inria-paris-robotics-lab/wireless-e-stop/images/NANO-nRF24L01.png

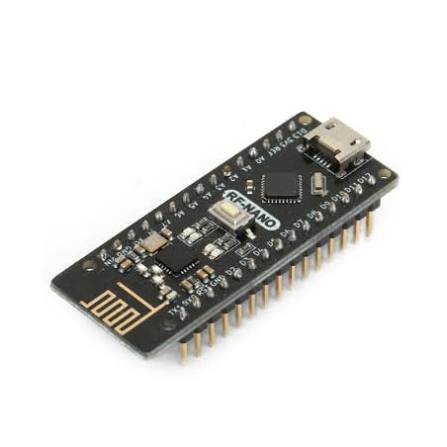
images/NANO-nRF24L01.png
