inria-paris-robotics-lab/wireless-e-stop/images/ws2812B.png

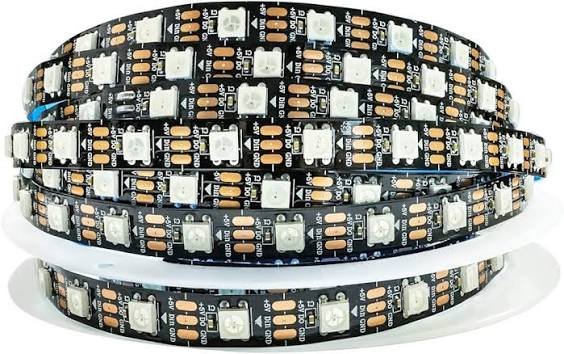
images/ws2812B.png
