inria-paris-robotics-lab/wireless-e-stop/hardware/Elec_schem/receiver/receiver.kicad_sch

## KiCad design hardware/Elec_schem/receiver/receiver.kicad_sch (2026-09-03)

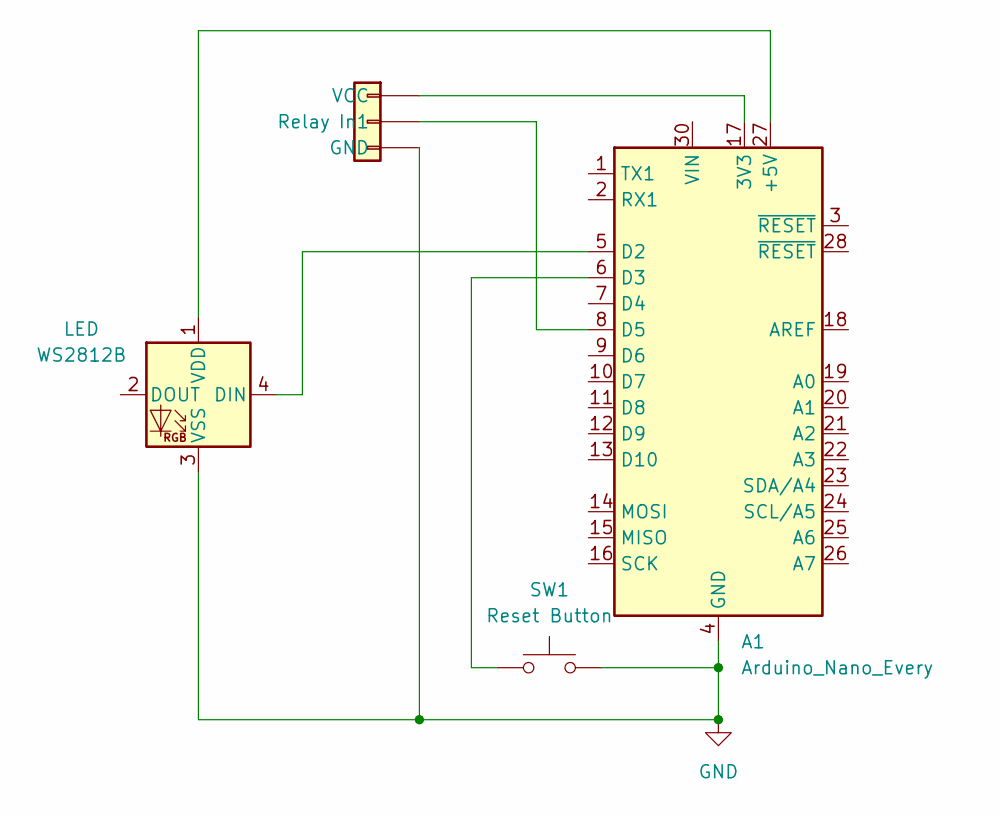
[picture p14: schematic receiver.kicad_sch]

Parts:
A1: Arduino_Nano_Every; Arduino_Nano
LED: WS2812B; LED_WS2812B_PLCC4_5.0x5.0mm_P3.2mm
Relay: Relay
SW1: Reset Button

Connections:
GND: A1.4 (GND), A1.29 (GND), LED.3 (VSS), Relay.3 (GND), SW1.2
unnamed: A1.5 (D2), LED.4 (DIN)
unnamed: A1.6 (D3), SW1.1
unnamed: A1.8 (D5), Relay.2 (In1)
unnamed: A1.17 (3V3), Relay.1 (VCC)
unnamed: A1.27 (+5V), LED.1 (VDD)
