inria-paris-robotics-lab/wireless-e-stop/hardware/Elec_schem/transmitter/transmitter.kicad_sch

## KiCad design hardware/Elec_schem/transmitter/transmitter.kicad_sch (2026-09-03)

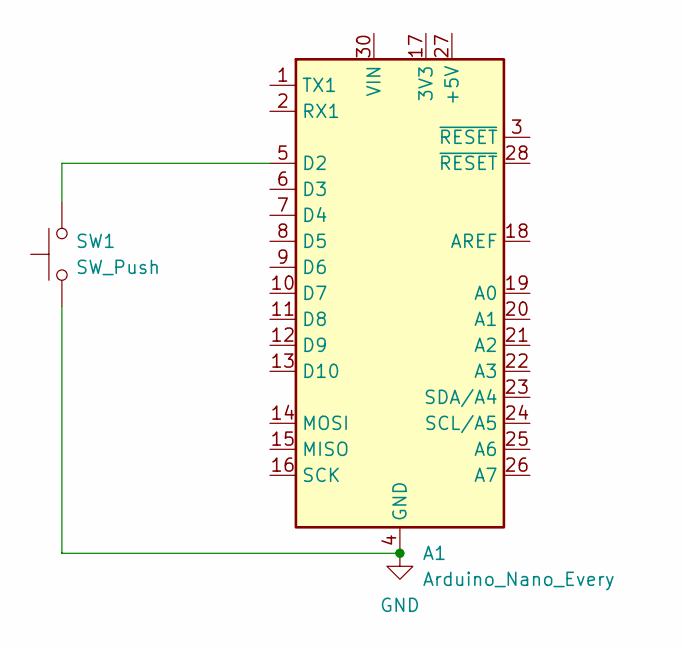
[picture p15: schematic transmitter.kicad_sch]

Parts:
A1: Arduino_Nano_Every; Arduino_Nano
SW1: SW_Push

Connections:
GND: A1.4 (GND), A1.29 (GND), SW1.1
unnamed: A1.5 (D2), SW1.2
